partlyhuman/QV1ckenIR/firmware/wqv12/include/Nokia_Cellphone_FC_8.h

const uint8_t Nokia_Cellphone_FC_8Bitmaps[] PROGMEM = {
0x00, 0xDB, 0x6C, 0x30, 0xAA, 0x53, 0xEF, 0x94, 0xFB, 0xE5, 0x00, 0x51, 0xED, 0x3C, 0x79, 0x6F, 0x14, 0xC9, 0xB0, 0x41, 0x82, 0x0D, 0x93, 0x00, 0x71, 0xB1, 0xC7, 0xAD, 0xDB, 0x9D, 0x00, 0xA0, 0x24, 0xCC, 0xCC, 0x42, 0x84, 0x66, 0x66, 0x48, 0x22, 0xAF, 0x9C, 0xFA, 0xA2, 0x00, 0x20, 0x8F, 0x88, 0x20, 0x5A, 0x00, 0xF0, 0xD8, 0x22, 0x64, 0xC8, 0x80, 0x73, 0x6D, 0xB6, 0xDB, 0x67, 0x00, 0x6E, 0x66, 0x66, 0x60, 0xF0, 0x61, 0x9C, 0xC3, 0x0F, 0x80, 0xF0, 0x61, 0x9C, 0x18, 0x6F, 0x00, 0x18, 0xE5, 0xA6, 0xF8, 0x61, 0x80, 0xF2, 0x0F, 0x06, 0x18, 0x6F, 0x00, 0x73, 0x0F, 0x36, 0xDB, 0x67, 0x00, 0xF8, 0x63, 0x0C, 0x61, 0x86, 0x00, 0x73, 0x6D, 0x9C, 0xDB, 0x67, 0x00, 0x73, 0x6D, 0xB6, 0x78, 0x67, 0x00, 0xD8, 0x6C, 0xD8, 0x2D, 0x00, 0x11, 0x99, 0x86, 0x18, 0x40, 0xF0, 0x3C, 0x86, 0x18, 0x66, 0x62, 0x00, 0xF0, 0x63, 0x18, 0x60, 0x06, 0x00, 0x79, 0x9B, 0xF6, 0xEF, 0xD8, 0x1E, 0x00, 0x73, 0x6D, 0xB6, 0xFB, 0x6D, 0x80, 0xF3, 0x6F, 0x36, 0xDB, 0x6F, 0x00, 0x7B, 0x0C, 0x30, 0xC3, 0x07, 0x80, 0xF3, 0x6D, 0xB6, 0xDB, 0x6F, 0x00, 0xFB, 0x0F, 0x30, 0xC3, 0x0F, 0x80, 0xFB, 0x0F, 0x30, 0xC3, 0x0C, 0x00, 0x73, 0x0C, 0x36, 0xDB, 0x67, 0x80, 0xDB, 0x6F, 0xB6, 0xDB, 0x6D, 0x80, 0xDB, 0x6D, 0xB0, 0x31, 0x8C, 0x63, 0x1B, 0x80, 0xCD, 0xB3, 0xC7, 0x0F, 0x1B, 0x33, 0x00, 0xC6, 0x31, 0x8C, 0x63, 0xC0, 0x82, 0xC6, 0xEE, 0xFE, 0xD6, 0xC6, 0xC6, 0x8D, 0x9B, 0xB7, 0xED, 0xD9, 0xB1, 0x00, 0x79, 0x9B, 0x36, 0x6C, 0xD9, 0x9E, 0x00, 0xF3, 0x6D, 0xB6, 0xF3, 0x0C, 0x00, 0x79, 0x9B, 0x36, 0x6C, 0xDB, 0x9E, 0x06, 0xF3, 0x6D, 0xB6, 0xF3, 0x4D, 0x80, 0x76, 0x30, 0xC3, 0x1B, 0x80, 0xFC, 0x60, 0xC1, 0x83, 0x06, 0x0C, 0x00, 0xDB, 0x6D, 0xB6, 0xDB, 0x67, 0x00, 0xCD, 0x9B, 0x33, 0xC7, 0x86, 0x0C, 0x00, 0xC6, 0xC6, 0xD6, 0xFE, 0x7C, 0x7C, 0x6C, 0xCD, 0x99, 0xE1, 0x87, 0x99, 0xB3, 0x00, 0xCD, 0x99, 0xE1, 0x83, 0x06, 0x0C, 0x00, 0xF8, 0x63, 0x9C, 0xE3, 0x0F, 0x80, 0xEC, 0xCC, 0xCC, 0xCE, 0x88, 0xC4, 0x62, 0x20, 0xE6, 0x66, 0x66, 0x6E, 0x4E, 0xA0, 0xFC, 0x88, 0x70, 0x67, 0xB6, 0x78, 0xC3, 0x0F, 0x36, 0xDB, 0x6F, 0x00, 0x76, 0x31, 0x87, 0x00, 0x18, 0x67, 0xB6, 0xDB, 0x67, 0x80, 0x73, 0x6F, 0xB0, 0x78, 0x6C, 0xEC, 0xCC, 0xC0, 0x7B, 0x6D, 0x9E, 0x19, 0xC0, 0xC3, 0x0F, 0x36, 0xDB, 0x6D, 0x80, 0xC3, 0x6D, 0xB0, 0x60, 0x66, 0x66, 0x6C, 0xC3, 0x0D, 0xBC, 0xE3, 0xCD, 0x80, 0xDB, 0x6D, 0xB0, 0xFE, 0x6D, 0xB6, 0xDB, 0x6D, 0xB0, 0xF3, 0x6D, 0xB6, 0xD8, 0x73, 0x6D, 0xB6, 0x70, 0xF3, 0x6D, 0xBC, 0xC3, 0x00, 0x7B, 0x6D, 0x9E, 0x18, 0x60, 0xD7, 0xB1, 0x8C, 0x00, 0x76, 0x3C, 0x6E, 0x00, 0xCC, 0xEC, 0xCC, 0x60, 0xDB, 0x6D, 0xB6, 0x78, 0xDB, 0x67, 0x1C, 0x20, 0xC6, 0xD6, 0xD6, 0x7C, 0x6C, 0xDB, 0x67, 0x36, 0xD8, 0xDB, 0x6D, 0x9E, 0x19, 0xC0, 0xF8, 0xC6, 0x30, 0xF8, 0xEC, 0xCC, 0xCC, 0xCE, 0xDB, 0x6D, 0xB6, 0xE6, 0x66, 0x66, 0x6E, 0x6A, 0xC0
};
const GFXglyph Nokia_Cellphone_FC_8Glyphs[] PROGMEM = {
	{	0,	3,	1,	3,	0,	-7},
	{	1,	3,	7,	3,	0,	-6},
	{	4,	4,	2,	4,	0,	-6},
	{	5,	6,	7,	6,	0,	-6},
	{	11,	6,	8,	6,	0,	-6},
	{	17,	7,	7,	7,	0,	-6},
	{	24,	7,	7,	7,	0,	-6},
	{	31,	2,	2,	2,	0,	-6},
	{	32,	4,	8,	4,	0,	-6},
	{	36,	4,	8,	4,	0,	-6},
	{	40,	6,	7,	6,	0,	-6},
	{	46,	6,	5,	6,	0,	-5},
	{	50,	3,	3,	3,	0,	-1},
	{	52,	5,	1,	5,	0,	-3},
	{	53,	3,	2,	3,	0,	-1},
	{	54,	4,	7,	4,	0,	-6},
	{	58,	6,	7,	6,	0,	-6},
	{	64,	4,	7,	4,	0,	-6},
	{	68,	6,	7,	6,	0,	-6},
	{	74,	6,	7,	6,	0,	-6},
	{	80,	6,	7,	6,	0,	-6},
	{	86,	6,	7,	6,	0,	-6},
	{	92,	6,	7,	6,	0,	-6},
	{	98,	6,	7,	6,	0,	-6},
	{	104,	6,	7,	6,	0,	-6},
	{	110,	6,	7,	6,	0,	-6},
	{	116,	3,	5,	3,	0,	-4},
	{	118,	3,	6,	3,	0,	-4},
	{	121,	5,	7,	5,	0,	-6},
	{	126,	5,	3,	5,	0,	-3},
	{	128,	5,	7,	5,	0,	-6},
	{	133,	6,	7,	6,	0,	-6},
	{	139,	7,	7,	7,	0,	-5},
	{	146,	6,	7,	6,	0,	-6},
	{	152,	6,	7,	6,	0,	-6},
	{	158,	6,	7,	6,	0,	-6},
	{	164,	6,	7,	6,	0,	-6},
	{	170,	6,	7,	6,	0,	-6},
	{	176,	6,	7,	6,	0,	-6},
	{	182,	6,	7,	6,	0,	-6},
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
};
const GFXfont Nokia_Cellphone_FC_8 PROGMEM = {
    (uint8_t *)Nokia_Cellphone_FC_8Bitmaps,
    (GFXglyph *)Nokia_Cellphone_FC_8Glyphs,
    0x20, 0x7E, 8};
